any-cubes/any-cubes/cubes/light-cube/code/light-cube/credentials_example.h

// 1. Duplicate this file and rename it to `credentials.h`
// 2. Uncomment the lines below
// 3. Replace the placeholder strings below with your credentials

//const char* ssid = "NETWORK_SSID";
//const char* password = "NETWORK_PASSWORD";
//const char* mqttServer = "IP_ADDRESS_OF_THE_MQTT_SERVER";
//const char* mqttUsername = "MQTT_USERNAME";
//const char* mqttPassword = "MQTT_PASSWORD";
